timdrysdale/atmega-demo/doc/2002271813_XKB-Connectivity-U-E-051N-4BH21-F1B_C381142.pdf

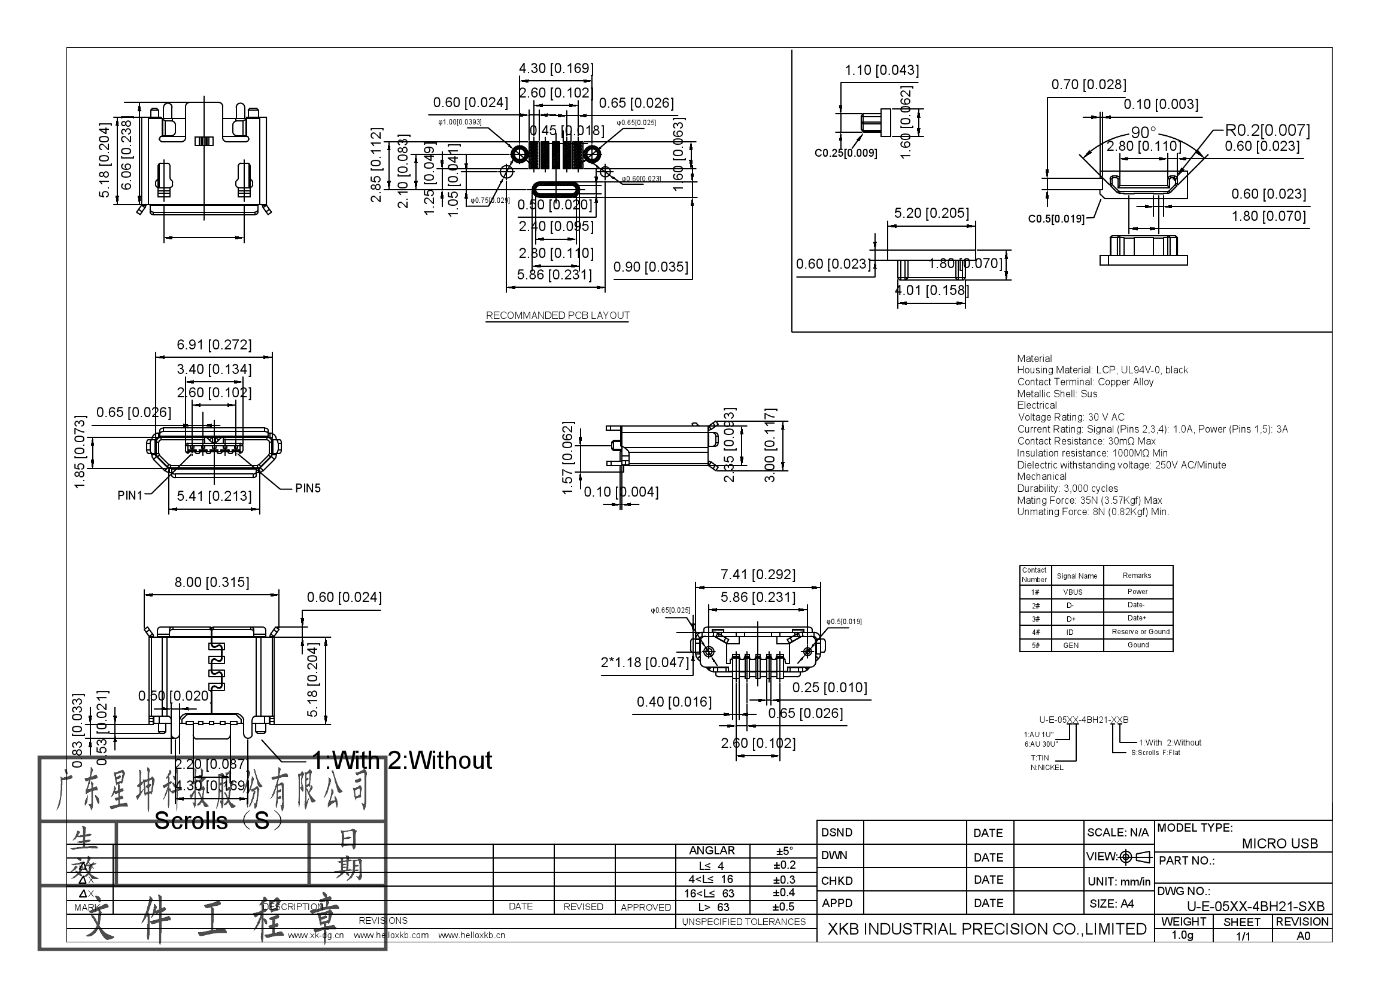
[picture p8: page 1]
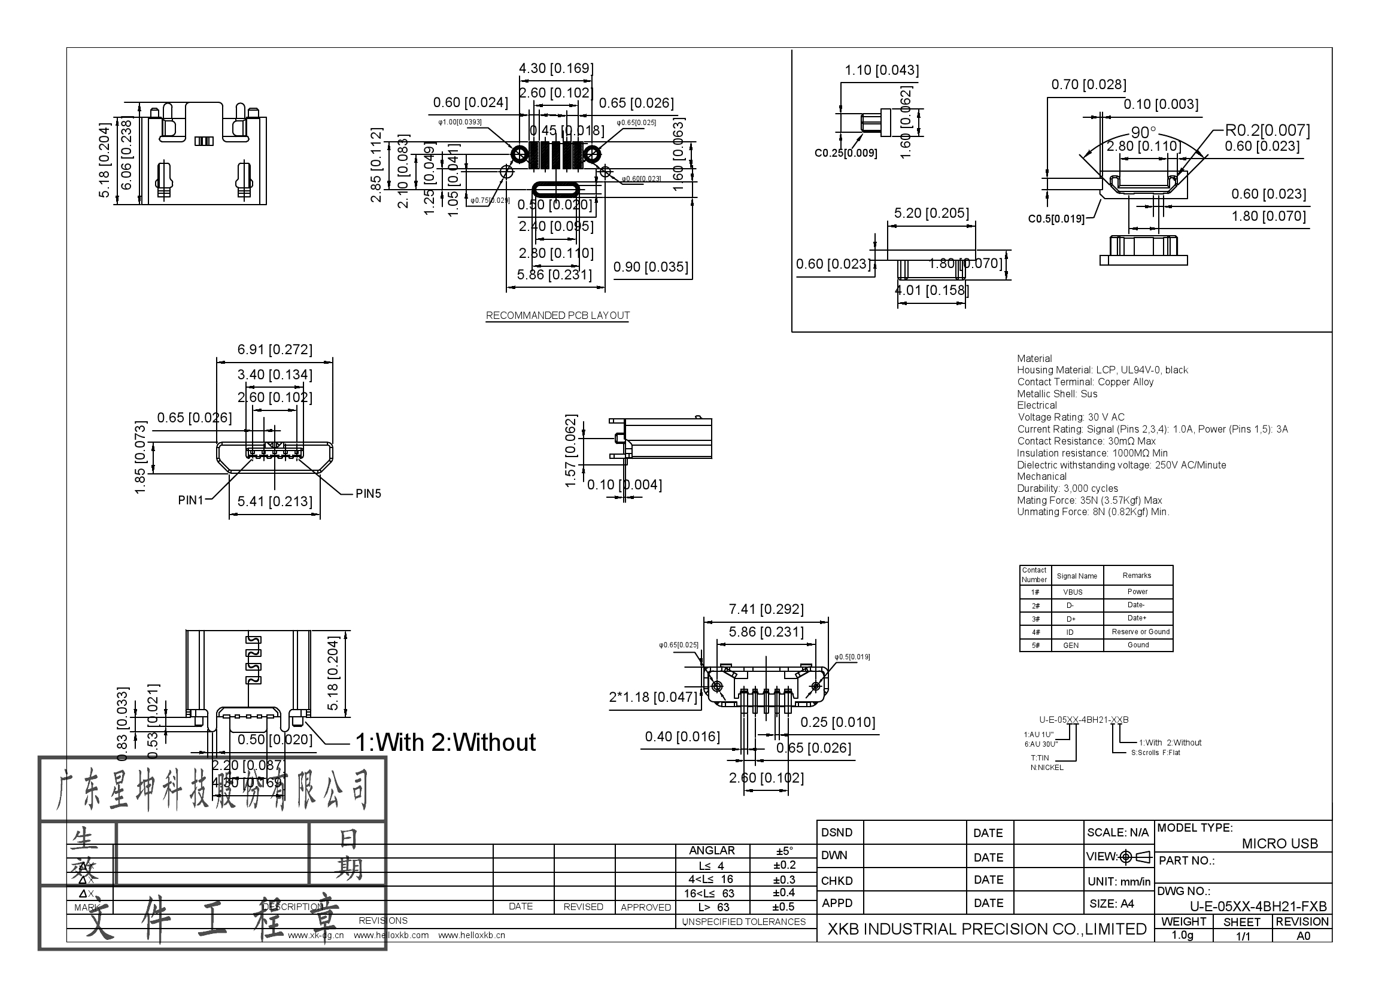
[picture p9: page 2]
